sharst/OpenHumidor-Hardware/CircuitBoards/openhum6-mega/gerber/back.png

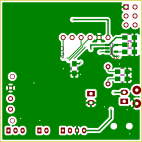
CircuitBoards/openhum6-mega/gerber/back.png
