sharst/OpenHumidor-Hardware/CircuitBoards/openhum6-mega/openhum6-mega-assembly-back.png

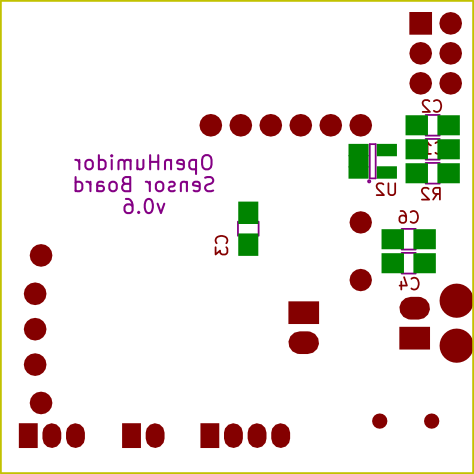
CircuitBoards/openhum6-mega/openhum6-mega-assembly-back.png
