sharst/OpenHumidor-Hardware/CircuitBoards/openhum6-mega/openhum6-mega-assembly-front.png

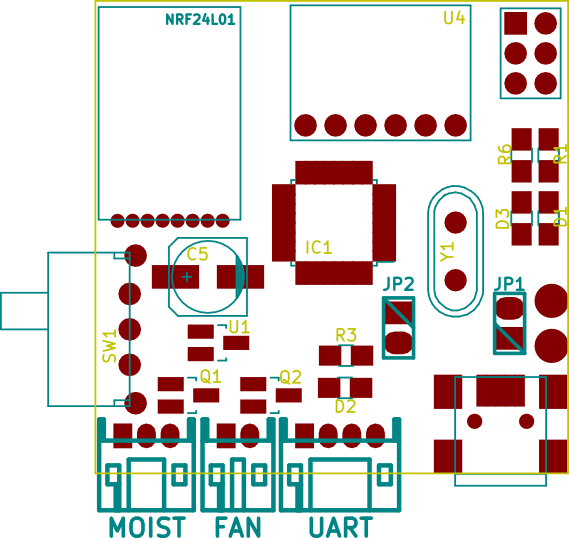
CircuitBoards/openhum6-mega/openhum6-mega-assembly-front.png
